Shaurya-Ashu/Functional-Hub/PCB/BOTTOM.png

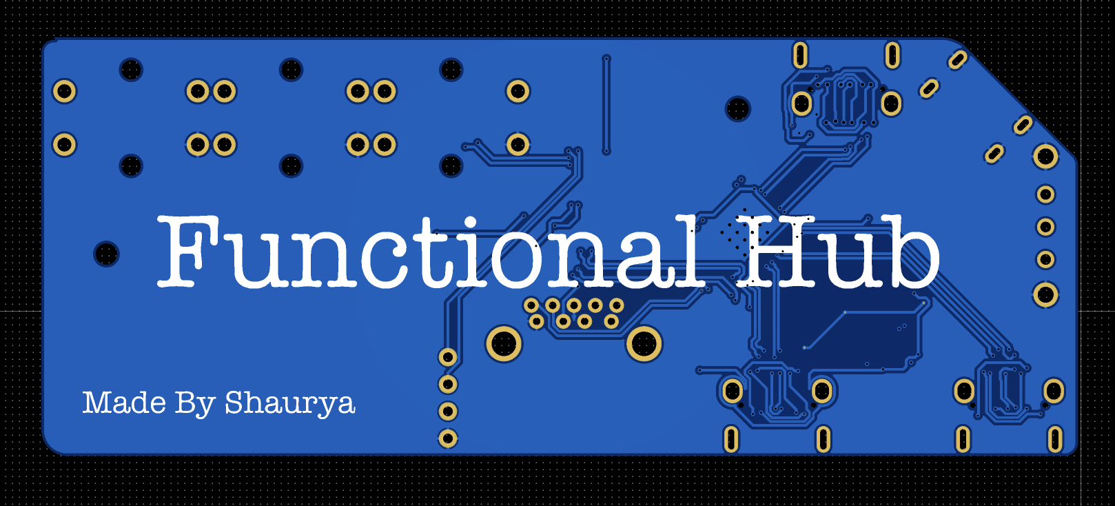
PCB/BOTTOM.png
