Shaurya-Ashu/Functional-Hub/PCB/Full Stack.png

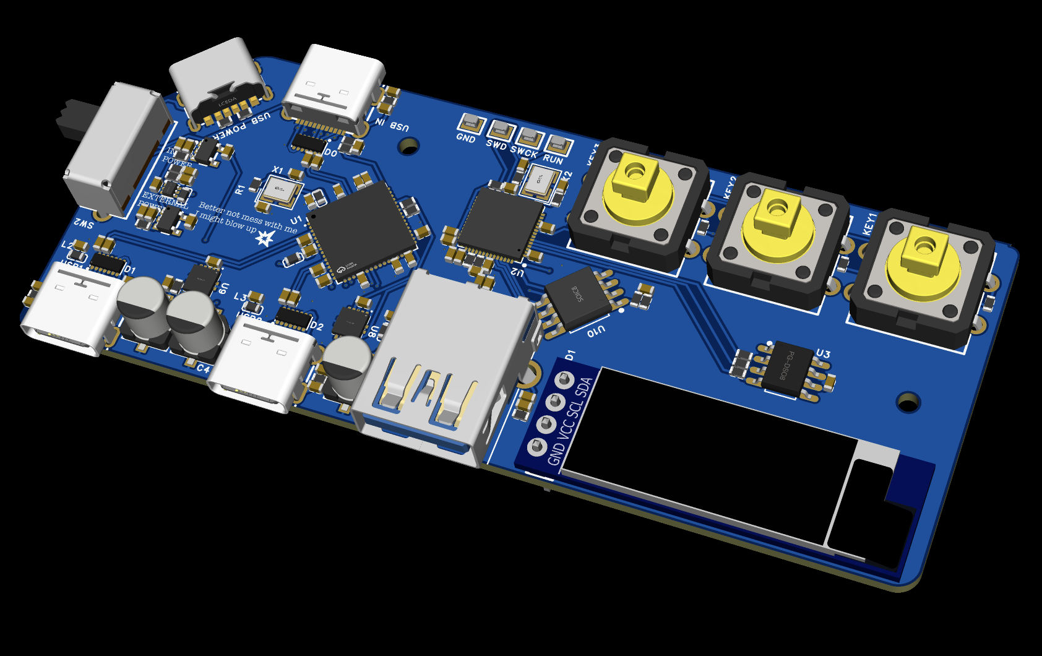
PCB/Full Stack.png
