Shaurya-Ashu/Functional-Hub/Assembly/Bottom Base.png

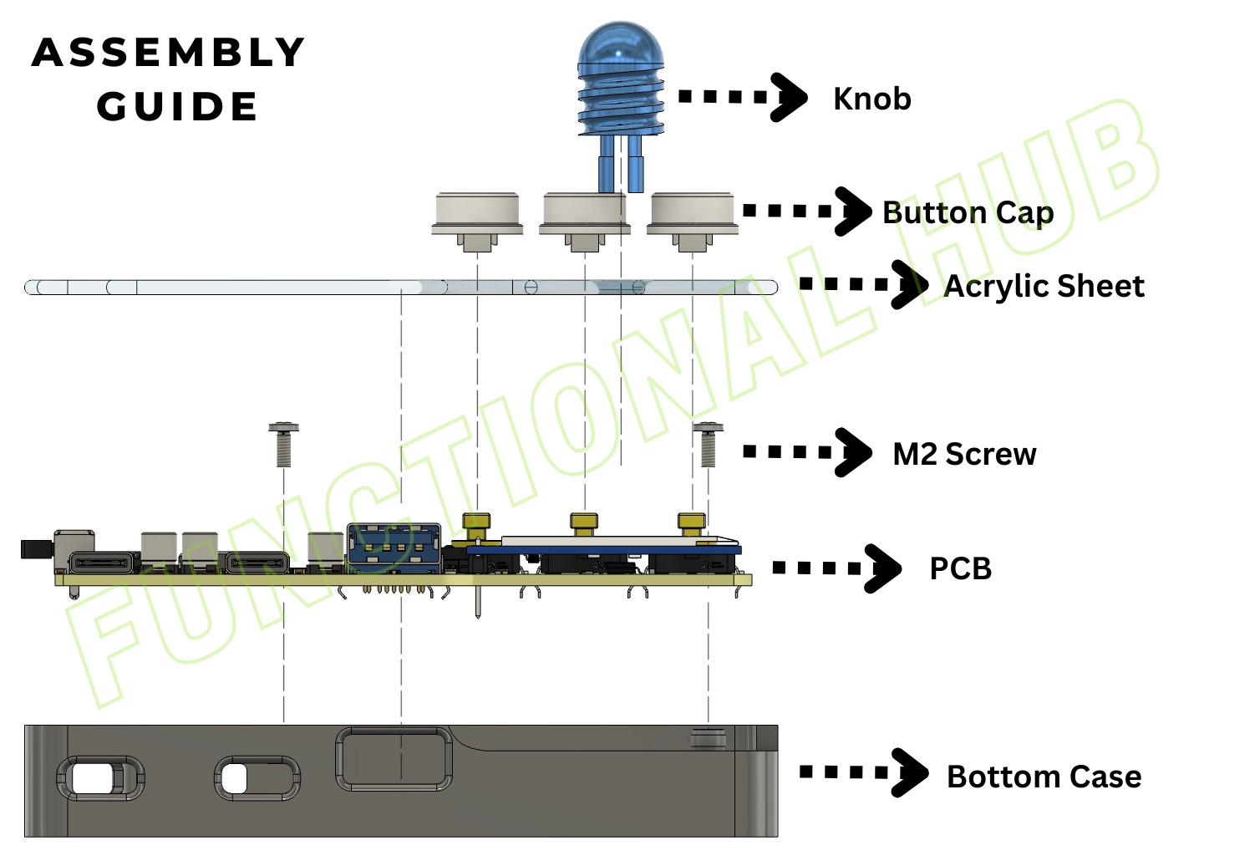
Assembly/Bottom Base.png
